ErenYagar/nvidia-lde-orcad-portfolio/evidence/stage3/3d_status.md

# Stage 3 RevK mechanical status

Disposition：`Digital_MCAD_Review_Complete_With_Explicit_Model_Blockers`

RevK native board SHA-256：`C772E9C3CD7A04A2CE3FBD1F5AE659E0935B786B235B17354DB83371BB4FF3EA`

RevK 3DX Canvas直接顯示：

- unplaced components 0/61；
- unrouted nets 0/54；
- unrouted connections 0/197；
- shape islands 0；
- unassigned shapes 0；
- DRC status up to date；DRC errors 0；shorting errors 0。

Assembly STEP：

- path：`manufacturing/stage3_final_revk/pcie_gen3_x4_nvme_adapter_reva_revk_final_preliminary.step`
- SHA-256：`DB176B106DC8D612EBFF79B8306FD327B831017CC22861F32DA83B99DF441EE0`
- size：8,939,536 bytes；
- format：STEP AP242；units：mm；datum：TOP/UPPER；
- isolated native DRA assignment/readback：`NATIVE_DRA_STEP_ASSIGNMENT_OK`。

`evidence/stage3/3dx_native_revk/`保存目前RevK工具畫面；`evidence/stage3/portfolio_revk/`的黑背景圖為presentation carry-forward。RevI到RevK之間的外部placement/model geometry未變，只有內層power connectivity vias與shape closure變更，因此可用於面試視覺，但不能當作exact-model collision Pass證據。

3D-01～3D-08仍依exact model可用性維持`Preliminary_Clear`或`Blocked_Missing_Exact_Model`。不宣稱PCIe compliance、fabrication release、chassis compatibility或bench qualification。
