ErenYagar/nvidia-lde-orcad-portfolio/evidence/stage3/final_release_status.md

# RevK final release status

`Interview_Digital_Complete` is achieved for the OrCAD digital portfolio.

`Fabrication_Ready` remains false because the project does not yet have the current fabricator stack-up, governing controlled specifications, frozen impedance geometry, exact mechanical context or physical bring-up evidence.

The digital closure is supported by the RevK native audits, current-board 3DX captures, AP242 STEP export and native re-import, engineering manufacturing outputs, PSpice failure/runtime-limit disclosure and hash-bound manifests.

No PCIe compliance, universal SSD support, chassis compatibility or bench qualification is claimed.
