ErenYagar/nvidia-lde-orcad-portfolio/evidence/stage3/stage3_delivery_gate.md

# Stage 3 RevK delivery gate

- Interview digital closure：`COMPLETE`
- Candidate status：`Interview_Digital_Complete_Not_For_Fabrication`
- Fabrication release：`BLOCKED`
- Native DRC：0
- Unconnected connections：0
- Active rats：0
- Unconnected PCIe nets：0
- Shape islands：0
- Unassigned shapes：0
- Native differential pairs：9（每組2 members）
- Pending fabricator geometry：9 pairs
- Exact-model collision blockers：仍存在
- PSpice governing recovery：`Simulated_Fail`（3.109 V）
- PSpice candidate sweep：27 × `Not_Concluded_Runtime_Limit`

## Digital gate results

- [x] RevK native board exists and is hash-bound。
- [x] DRC / connectivity / rats / PCIe connectivity closed。
- [x] L2/L5 GND與L4 power shapes implemented；zero islands。
- [x] 9 native differential pairs established。
- [x] Current RevK native 3DX evidence captured。
- [x] AP242/mm STEP generated and assigned/read back in isolated native DRA。
- [x] 14 Gerber、2 NC Drill、IPC-2581、BOM、P&P與CAM previews generated。
- [x] IPC-356 empty result excluded；ODB++ install limitation disclosed。
- [x] PSpice failure/runtime limitations disclosed without false pass。

## Fabrication blockers

- [ ] JLCPCB controlled-impedance stack-up archived。
- [ ] PCIe CEM/M.2 controlled specification sign-off completed。
- [ ] Pair width/gap/via geometry frozen in Constraint Manager。
- [ ] Exact mechanical models and 3D-01～3D-08 closure completed。
- [ ] Final CAM/DFM review after the above ECOs。
- [ ] Physical fabrication and bring-up completed。

Manufacturing files are engineering-review outputs only and must not be uploaded for fabrication while these gates remain open。
