ErenYagar/nvidia-lde-orcad-portfolio/portfolio/index.html

▰ EREN YAGAR / BOARD DESIGN

NVIDIA LDE INTERVIEW PORTFOLIO · REV K

# PCIe × NVMe without the black box.

A traceable OrCAD X / Allegro workflow for a six-layer PCIe Gen3 x4 add-in card to M.2 M-Key 2280 NVMe adapter.

See what it does ↘Read the case study ↗

INTERVIEW_DIGITAL_COMPLETE/Preliminary mechanical + digital review

FIG 01 / ASSEMBLY

120 × 64 MM · 6L

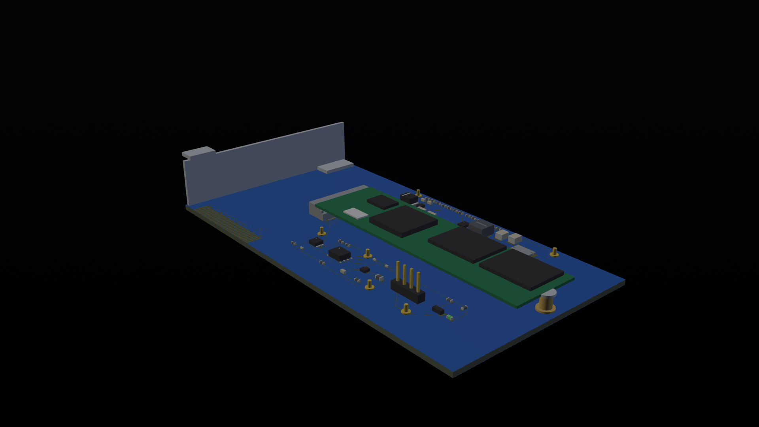
[picture p1: evidence/stage3/portfolio_revk/stage3_hero_isometric_assembly.png]
Isometric 3D assembly view of the PCIe to M.2 NVMe adapter board


06copper layers

×4PCIe Gen3 lanes

5A3.3 V normal target

09native pair objects

01 / SYSTEM FUNCTION

## A physical bridge, not a protocol box.

The host Root Complex and the NVMe controller remain the protocol endpoints. This board owns connection, power, telemetry and reviewable handoff.

HOSTPCIe Root ComplexJ1 edge · lanes / REFCLK

→

BOARDSix-layer interposerpower · sensing · placement

→

SSDM.2 M-Key 2280J2 · NVMe endpoint

01

### Signal continuity

Eight data pairs, REFCLK and sidebands are defined as a direct host-to-SSD path. No retimer, switch or packet conversion.

02

### Protected power

12 V slot input passes an eFuse, 6 A buck and 5 mΩ Kelvin shunt before the 3.3 V SSD branch.

03

### Observable rails

INA238 current and TMP1075 temperature paths reach a target-only I²C header with no external power back-feed.

04

### Explicit boundary

Digital closure is complete for the current board; compliance, chassis fit and bench qualification remain open.

02 / VISUAL EVIDENCE

## Designed to be inspected.

Portfolio views stay clean; engineering views, native reports and hashes remain in the repository.

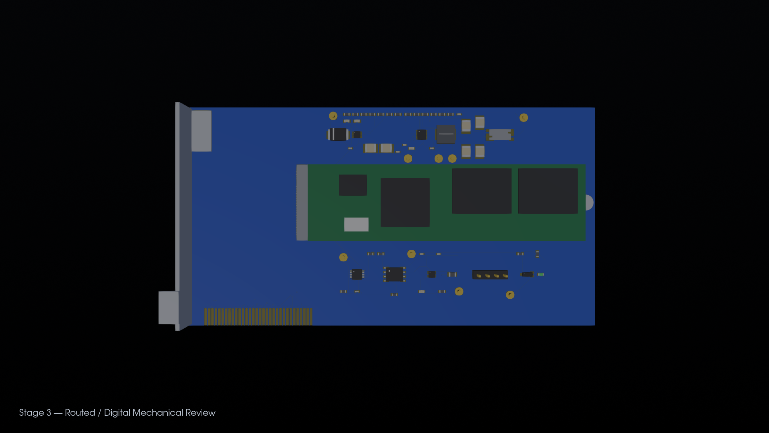
[picture p2: evidence/stage3/portfolio_revk/stage3_top_assembly.png]
Top assembly view showing M.2 slot, PCIe edge connector and component placement
 VIEW FULL ↗

02 / TOP ASSEMBLYConnector-first placement

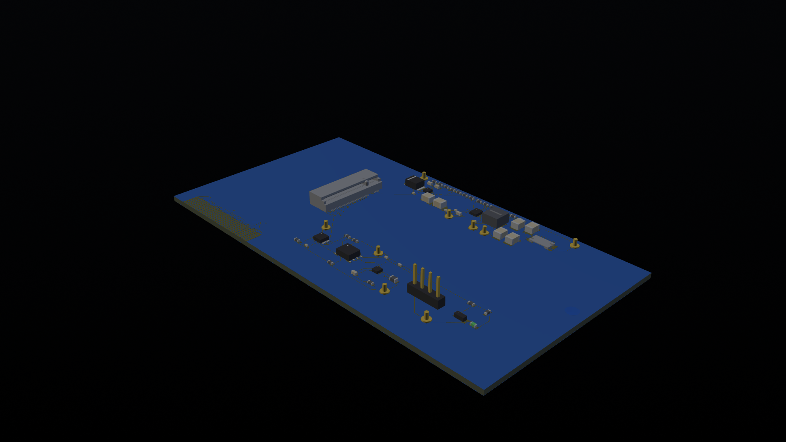
[picture p3: evidence/stage3/portfolio_revk/stage3_hero_isometric_pcb_detail.png]
Detailed isometric PCB view with component package models
 VIEW FULL ↗

03 / PACKAGE DETAILLibrary bodies, not blue blocks

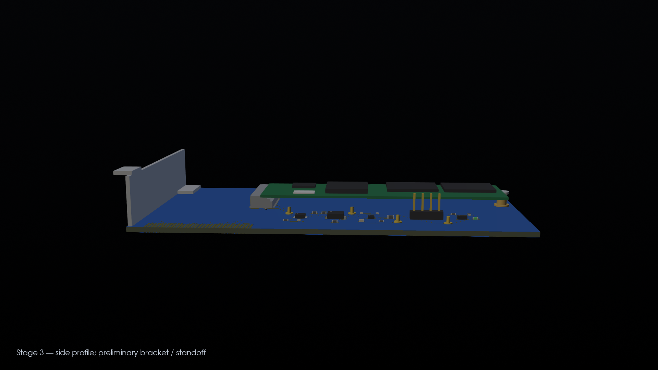
[picture p4: evidence/stage3/portfolio_revk/stage3_side.png]
Side view showing board thickness and low profile clearance
 VIEW FULL ↗

04 / SIDE REVIEWLow-profile baseline

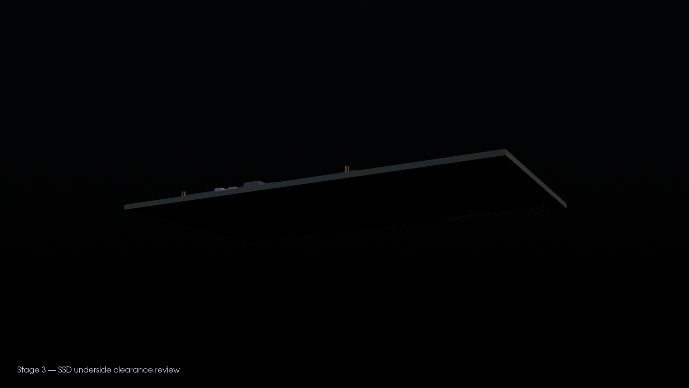
[picture p5: evidence/stage3/portfolio_revk/stage3_ssd_underside.png]
Underside view showing the SSD envelope and retention geometry
 VIEW FULL ↗

05 / UNDERSIDESSD envelope and retention

Open digital gate ↗Open native 3DX evidence ↗Open STEP status ↗

03 / ENGINEERING METHOD

## Every view has a paper trail.

The point is not to make uncertainty disappear; it is to make it findable.

01Power architecture

12 V + eFuse + buck was selected for review depth. The official buck profile records a 3.109 V recovery failure; no supported-SSD claim is inferred.

Read decision record ↗

02High-speed intent

Nine native differential-pair objects exist. Width, gap, via and skew remain pending the actual fabricator stack-up and controlled spec.

Read constraint status ↗

033DX / STEP handoff

Native 3DX views and AP242/mm STEP re-import are hash-bound to RevK. Missing exact models keep collision cases preliminary or blocked.

Read 3D status ↗

04Automation boundary

Python validators test CSV/report contracts and negative fixtures; they do not replace native Cadence review or bench data.

Read test harness ↗

CURRENT REVK SNAPSHOT

### Closed digitally. Open physically.

DRC / connectivity0 / 0 / 0

3DX / STEP loopRecorded

PSpice recovery3.109 V · fail

Stack-up / pin freezeOpen gate

ENGINEERING BOUNDARY

## Honest status is part of the design.

- Not a fabrication release or PCIe compliance claim.
- Controlled CEM/M.2 pin sources and JLCPCB stack-up remain gates.
- PSpice recovery and exact-model collision limits stay visible.

SOURCE-TRACEABLE / REVIEW-READY

## Bring the board into the interview.

Start with the function. Open the evidence when the conversation turns technical.

Use the interview guide ↗View GitHub portfolio ↗ (https://github.com/ErenYagar/nvidia-lde-orcad-portfolio)

© 2026 Eren YagarOrCAD X / Allegro / PSpice / 3DXRepository README ↗

×
