ErenYagar/nvidia-lde-orcad-portfolio/evidence/stage3/3dx_native_revk/revk_isometric_with_ui.png

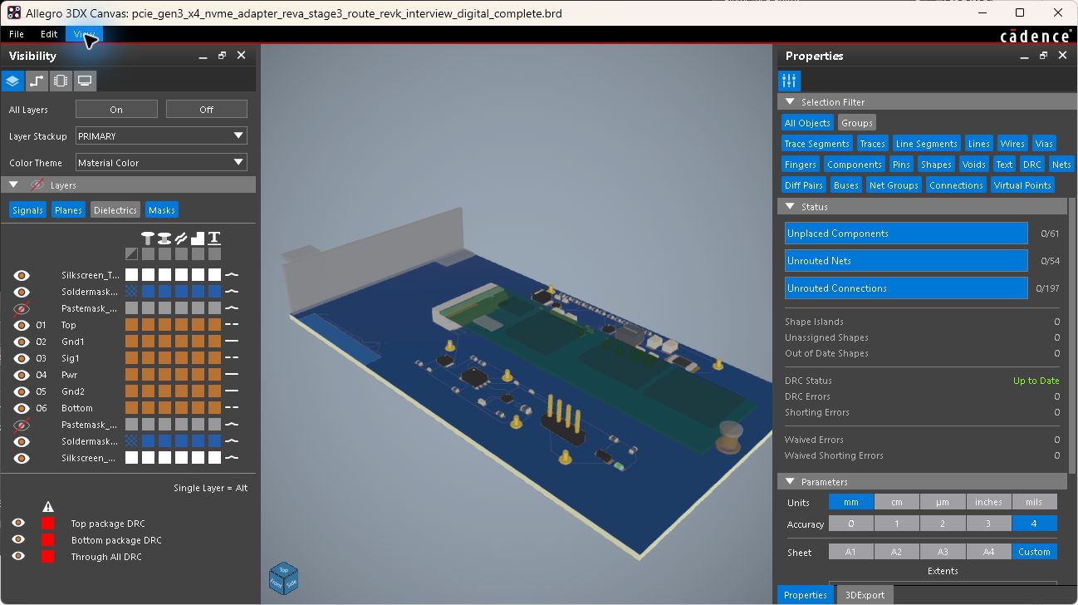
evidence/stage3/3dx_native_revk/revk_isometric_with_ui.png
