ErenYagar/nvidia-lde-orcad-portfolio/evidence/stage3/3dx_native_revk/revk_ssd_underside_bottom_iso_with_ui.png

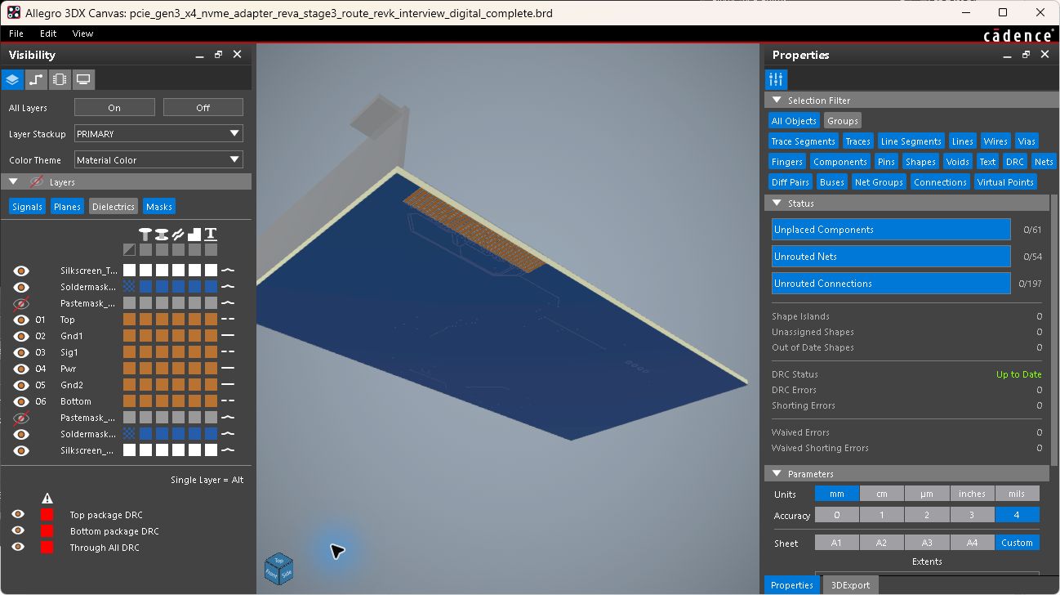
evidence/stage3/3dx_native_revk/revk_ssd_underside_bottom_iso_with_ui.png
