ErenYagar/nvidia-lde-orcad-portfolio/validation/supported_ssd_matrix.csv

Candidate_ID | Manufacturer | Exact_Model | Capacity_GB | Hardware_Revision | Firmware | Form_Factor | Steady_Current_A | Peak_Current_A | Peak_Duration_us | Power_Source_Type | Power_Source_Document | Power_Source_Revision | Power_Source_Date | Simulation_Evidence | Mechanical_Evidence | Bench_Evidence | Link_Evidence | Thermal_Evidence | Disposition | Exclusion_Reason | Reviewer | Review_Date | Official_Project_Status | Notes
WD-SN750-1TB-WDS100T3X0C | Western Digital | WDS100T3X0C | 1000 |  |  | M.2_2280_M_Key_NVMe |  | 2.8 | 10 | Official_Manufacturer | evidence/official_sources/WD_BLACK_SN750_Product_Brief_en_us.pdf | 02-05-WW-04-00054-A06 | 2021-09-01 | evidence/stage2/pspice/pw01_vendor_combined_run/pw01_window_metrics.csv |  |  |  |  | Candidate | Stage 2 PW-01 recovery minimum 3.109 V fails the 3.135 V screen; no support claim | Project | 2026-07-24 | Confirmed_Official | Stage 2 digital reference only; official brief confirms PCIe Gen3 x4 M.2 2280-S3-M 2.38 mm and 2.8 A peak for 10 us; candidate remains unqualified pending power-stage tuning and bench evidence
