ErenYagar/nvidia-lde-orcad-portfolio/evidence/stage3/portfolio_final_manifest.csv

Category | Path | Size_Bytes | SHA256 | Source_Board_SHA256 | Tool_Version | Export_Options | Artifact_State
Portfolio_View | evidence/stage3/portfolio_revk/stage3_bottom.png | 836241 | DD6D59DA8A34AD48E45E6F6496B7E7B3287F57D43F7E80EC34FC09076EDB2217 | C772E9C3CD7A04A2CE3FBD1F5AE659E0935B786B235B17354DB83371BB4FF3EA | Portfolio renderer | Black background; presentation carry-forward; external placement/models unchanged from RevI to RevK | Engineering_Assumption_Presentation_Only
Portfolio_View | evidence/stage3/portfolio_revk/stage3_bracket_review.png | 1134920 | 16A2DDD3E16E71FD604FCEED8EFF5096DB7E966670C49F217F7D0842DB3E07B3 | C772E9C3CD7A04A2CE3FBD1F5AE659E0935B786B235B17354DB83371BB4FF3EA | Portfolio renderer | Black background; presentation carry-forward; external placement/models unchanged from RevI to RevK | Engineering_Assumption_Presentation_Only
Portfolio_View | evidence/stage3/portfolio_revk/stage3_hero_isometric_assembly.png | 1068237 | 73D44483E89F8D3EC3DA486396125F33D81B8D2DE874CDA6AD81C6046A876B7F | C772E9C3CD7A04A2CE3FBD1F5AE659E0935B786B235B17354DB83371BB4FF3EA | Portfolio renderer | Black background; presentation carry-forward; external placement/models unchanged from RevI to RevK | Engineering_Assumption_Presentation_Only
Portfolio_View | evidence/stage3/portfolio_revk/stage3_hero_isometric_pcb_detail.png | 1047092 | 947E26D7545FA849B96110F3A6471BDFEC9349EE625C9F92349D176845722634 | C772E9C3CD7A04A2CE3FBD1F5AE659E0935B786B235B17354DB83371BB4FF3EA | Portfolio renderer | Black background; presentation carry-forward; external placement/models unchanged from RevI to RevK | Engineering_Assumption_Presentation_Only
Portfolio_View | evidence/stage3/portfolio_revk/stage3_side.png | 1122736 | AE649C2F9733FD281057A89A927F54B935771A81DF8F4056B75CFA0A47AC3A8A | C772E9C3CD7A04A2CE3FBD1F5AE659E0935B786B235B17354DB83371BB4FF3EA | Portfolio renderer | Black background; presentation carry-forward; external placement/models unchanged from RevI to RevK | Engineering_Assumption_Presentation_Only
Portfolio_View | evidence/stage3/portfolio_revk/stage3_ssd_underside.png | 1078659 | 9E7C0D50FCB859392D2BB6C93EDD4055487A906B86B05FCC9AA93C5AC043FF25 | C772E9C3CD7A04A2CE3FBD1F5AE659E0935B786B235B17354DB83371BB4FF3EA | Portfolio renderer | Black background; presentation carry-forward; external placement/models unchanged from RevI to RevK | Engineering_Assumption_Presentation_Only
Portfolio_View | evidence/stage3/portfolio_revk/stage3_top_assembly.png | 956764 | 278E7EC2BDE103E235BEA7C178F18A8CF67A20285036EA6B72F3E9F673CC8268 | C772E9C3CD7A04A2CE3FBD1F5AE659E0935B786B235B17354DB83371BB4FF3EA | Portfolio renderer | Black background; presentation carry-forward; external placement/models unchanged from RevI to RevK | Engineering_Assumption_Presentation_Only
Portfolio_View | evidence/stage3/portfolio_revk/stage3_top_pcb_detail.png | 941503 | 1F7E5A7ABA4ED7AF925F333A7F1F9B8C0B44121DCF040D93848C2527E408FFBA | C772E9C3CD7A04A2CE3FBD1F5AE659E0935B786B235B17354DB83371BB4FF3EA | Portfolio renderer | Black background; presentation carry-forward; external placement/models unchanged from RevI to RevK | Engineering_Assumption_Presentation_Only
