ErenYagar/nvidia-lde-orcad-portfolio/scripts/testdata/supported_ssd/valid/matrix.csv

Candidate_ID | Manufacturer | Exact_Model | Capacity_GB | Hardware_Revision | Firmware | Form_Factor | Steady_Current_A | Peak_Current_A | Peak_Duration_us | Power_Source_Type | Power_Source_Document | Power_Source_Revision | Power_Source_Date | Simulation_Evidence | Mechanical_Evidence | Bench_Evidence | Link_Evidence | Thermal_Evidence | Disposition | Exclusion_Reason | Reviewer | Review_Date | Official_Project_Status | Notes
TEST-CANDIDATE-01 | Example Storage | TEST-NVME-2280 | 1024 | A | TEST1 | M.2_2280_M_Key_NVMe | 4.0 | 6.0 | 100 | Official_Manufacturer | https://example.invalid/official-test-datasheet | TEST-REV-A | 2026-07-23 |  |  |  |  |  | Power_Screened |  |  |  | Confirmed_Official | Synthetic validator fixture only
TEST-EXCLUDED-01 | Example Storage | TEST-OVERLOAD | 2048 | A | TEST2 | M.2_2280_M_Key_NVMe | 5.5 | 8.0 | 150 | Official_Manufacturer | https://example.invalid/official-overload-test | TEST-REV-A | 2026-07-23 |  |  |  |  |  | Excluded | Exceeds project power envelope |  |  | Confirmed_Official | Synthetic validator fixture only
