ErenYagar/nvidia-lde-orcad-portfolio/scripts/testdata/stage2/invalid/missing_evidence/stage2/artifact_manifest.csv

Artifact | Path | Size_Bytes | SHA256 | Source_Path | Source_SHA256 | Status | Stage_State | Notes
Missing_Evidence | missing.bin | 1 | 0000000000000000000000000000000000000000000000000000000000000000 |  |  | Engineering_Assumption | Stage 2 - Batch Audited | Negative fixture
