ErenYagar/nvidia-lde-orcad-portfolio/scripts/testdata/stage2/invalid/stale_hash/stage2/artifact_manifest.csv

Artifact | Path | Size_Bytes | SHA256 | Source_Path | Source_SHA256 | Status | Stage_State | Notes
Stale_Hash | evidence.bin | 17 | 0000000000000000000000000000000000000000000000000000000000000000 |  |  | Engineering_Assumption | Stage 2 - Batch Audited | Negative fixture
