ErenYagar/nvidia-lde-orcad-portfolio/pcb/3d_models/stage3/harwin_s1751_46r.step

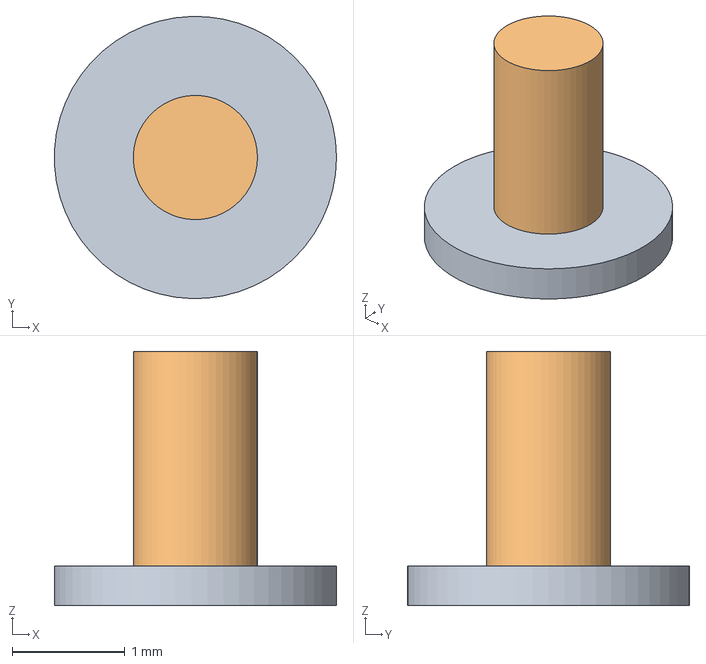
[picture p27: CAD file, 2026-07-27]
pcb/3d_models/stage3/harwin_s1751_46r.step
2.50 x 2.50 x 2.25 mm
