ErenYagar/nvidia-lde-orcad-portfolio/pcb/3d_models/stage3/r_0603_1608m.step

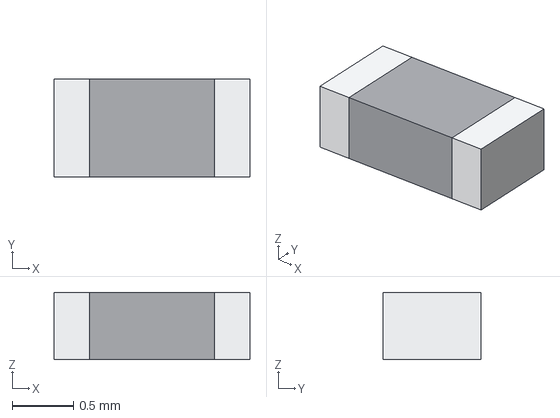
[picture p28: CAD file, 2026-07-27]
pcb/3d_models/stage3/r_0603_1608m.step
1.60 x 0.8 x 0.55 mm
