ErenYagar/nvidia-lde-orcad-portfolio/pcb/3d_models/stage3/c_1210_3225m.step

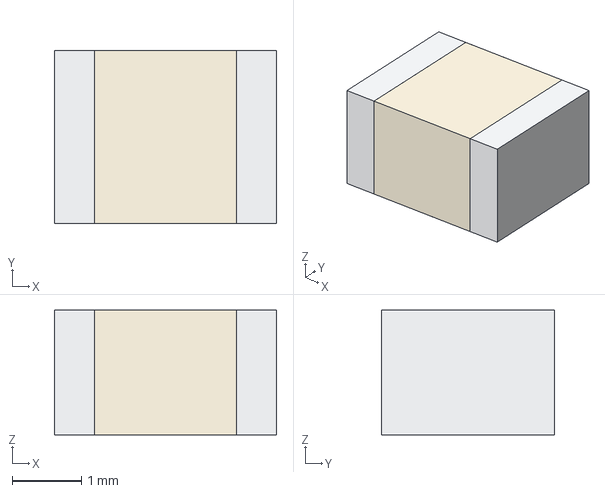
[picture p29: CAD file, 2026-07-27]
pcb/3d_models/stage3/c_1210_3225m.step
3.20 x 2.50 x 1.80 mm
