ErenYagar/nvidia-lde-orcad-portfolio/pcb/3d_models/stage3/hdr_1x4_2p54_ra.step

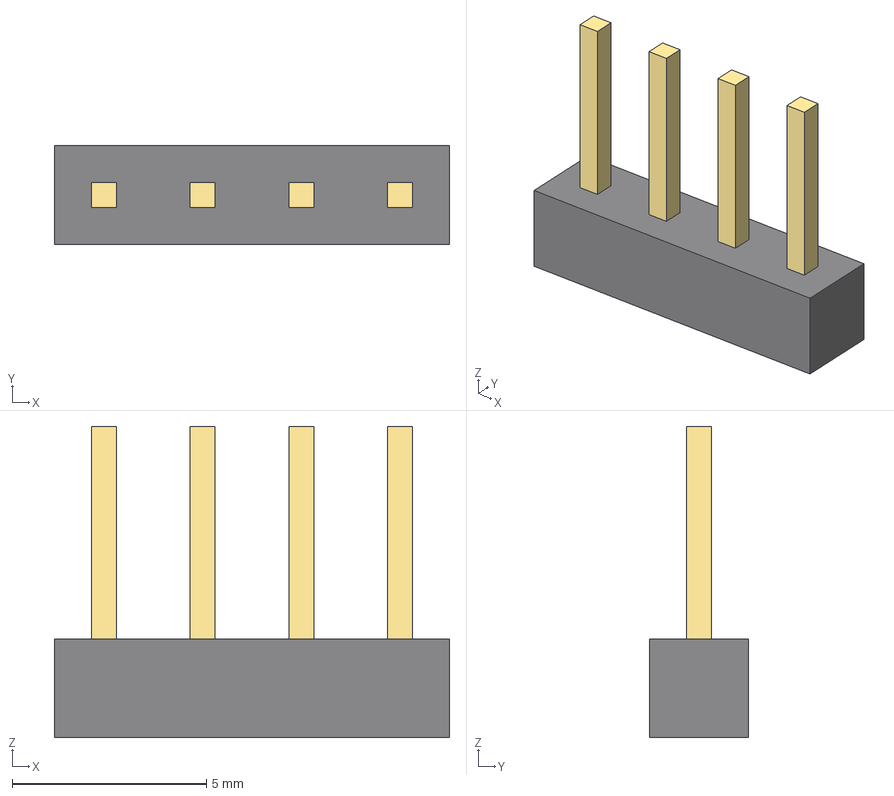
[picture p30: CAD file, 2026-07-27]
pcb/3d_models/stage3/hdr_1x4_2p54_ra.step
10.2 x 2.54 x 8.00 mm
