ErenYagar/nvidia-lde-orcad-portfolio/pcb/3d_models/stage3/low_profile_pcie_bracket_engineering.step

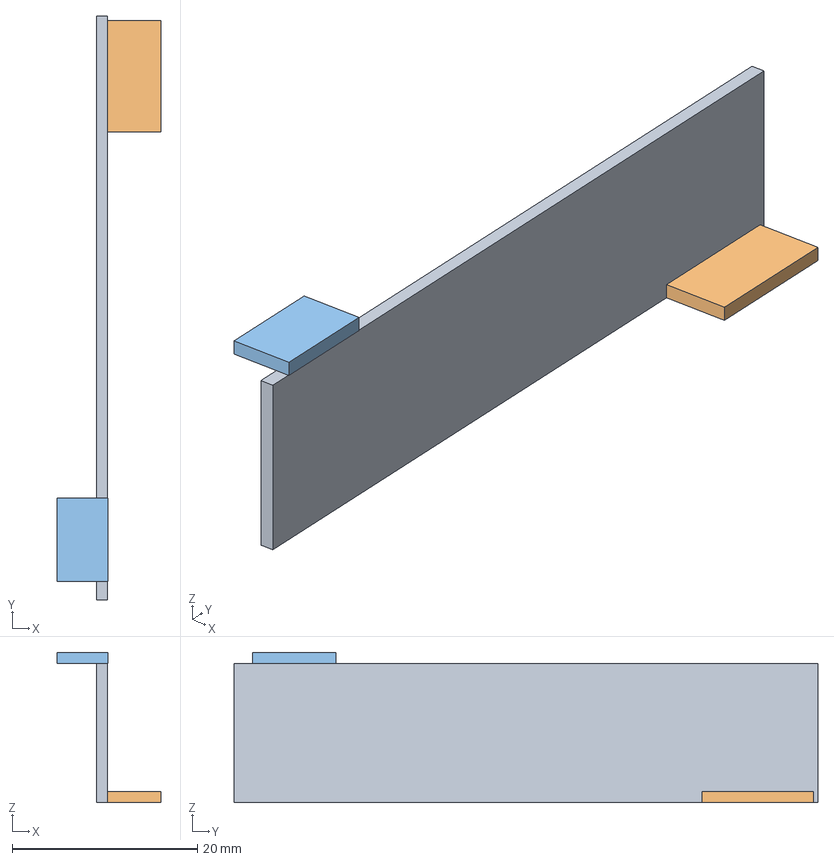
[picture p31: CAD file, 2026-07-27]
pcb/3d_models/stage3/low_profile_pcie_bracket_engineering.step
11.2 x 63.0 x 16.2 mm
