ErenYagar/nvidia-lde-orcad-portfolio/manufacturing/stage3_final_revk/cam_preview/revk_film_assembly_top_with_ui.png

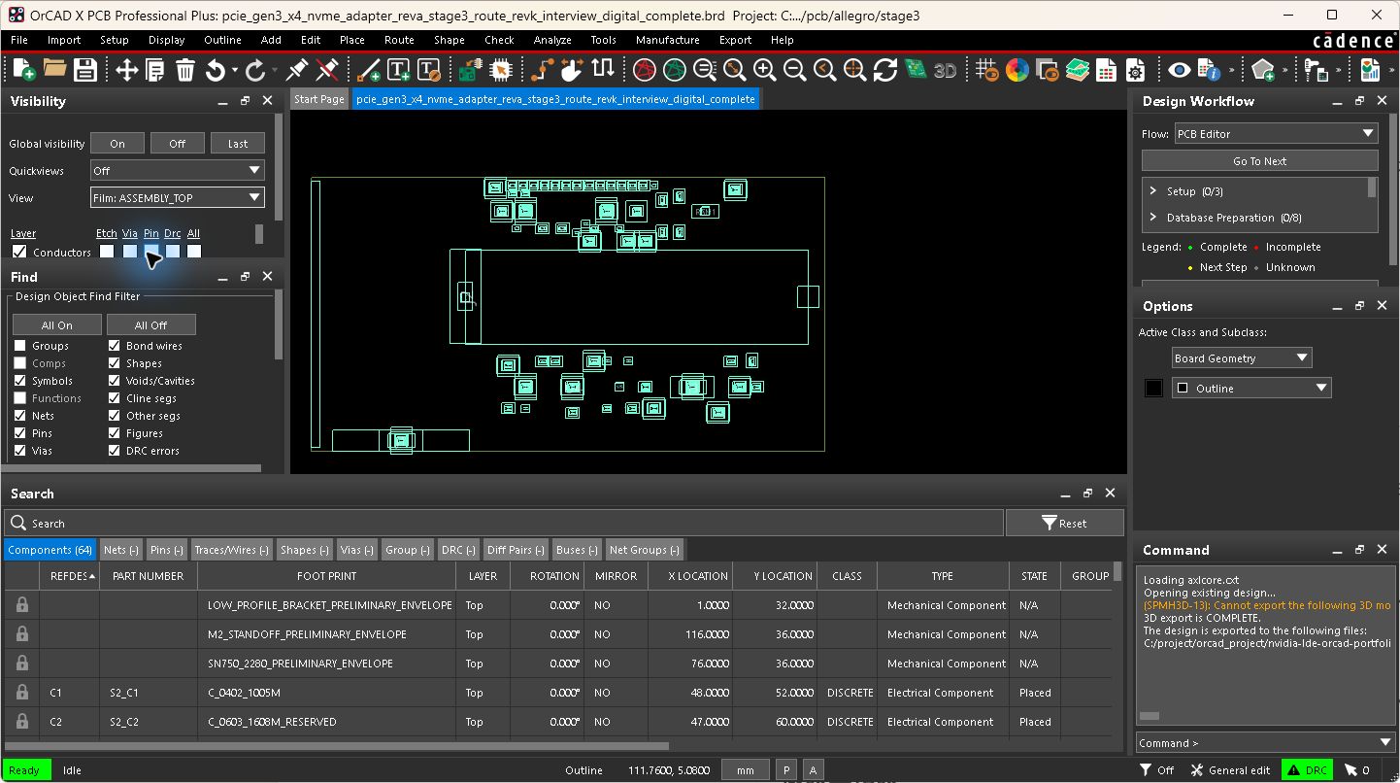
manufacturing/stage3_final_revk/cam_preview/revk_film_assembly_top_with_ui.png
