ErenYagar/nvidia-lde-orcad-portfolio/pspice/stage2/profile_results.csv

Profile_ID | Profile | Model | Input | Output | Raw_Result | Result | Status | Key_Observation | Limitations
ST-00 | Solver smoke test | PSpice primitive | evidence/stage2/batch/work/pspice_probe/pspice_probe.cir | evidence/stage2/batch/work/pspice_probe/pspice_probe.out | NA | Pass | Simulated | JOB CONCLUDED confirms the 25.1 command-line solver | Not a Rev A power-stage simulation
ST-02A | Buck startup through 820 us | TPS543620 SLUM787A | pspice/stage2/st02_buck_startup_820us.cir | pspice/stage2/st02_buck_startup_820us.out | pspice/stage2/st02_buck_startup_820us.csd | Partial_Startup_Concluded | Simulated | V(P3V3_NVME) final-window average 2.428 V while the 1 ms soft-start was still active | Does not evaluate steady state or the 7 A pulse
PW-01 | Combined startup and load sequence | TPS543620 SLUM787A | pspice/stage2/pw01_buck_combined_1400us.cir | pspice/stage2/pw01_buck_combined_1400us.out | pspice/stage2/pw01_buck_combined_1400us.csd | Fail_Recovery_Undershoot_5pct | Simulated | 5 A steady V(P3V3_NVME) minimum 3.149 V and 7 A/100 us minimum 3.204 V pass the 3.135 V screen; the recovery window minimum 3.109 V fails it while PGOOD remains high | Broad 5 A/7 A envelope is not qualified; peak inductor current reached 8.656 A; idealized macro-model omits layout and thermal effects; tune the power stage and rerun before any supported-SSD claim
LT-03S | Conservative 7 A charge-deficit capacitance sweep | PSpice primitive | evidence/stage2/batch/lt03_charge_deficit_summary.csv | evidence/stage2/batch/lt03_charge_deficit_summary.csv | evidence/stage2/batch/work/lt03_charge_deficit/ | Completed_Screen | Simulated | Six effective-Cout cases preserve the raw CSDF and threshold result | Not the official TPS543620 macro-model
EF-01 | eFuse isolated startup | TPS25947x SLVMDJ6A | pspice/smoke_tests/tps25947_vendor_reference/ | pspice/smoke_tests/tps25947_vendor_reference/run_record.md | pspice/smoke_tests/tps25947_vendor_reference/ | Fail_Functional_Validation | Pending_Human_Verification | Encrypted model loaded but retained runs did not reach a valid output startup | No eFuse startup inrush or latch-off claim
AC-01 | Loop stability | TPS543620 SLUM787A | NA | pspice/simulation_plan.md | NA | Not_Supported_By_Model | Planned | Transient encrypted model has no supported average or small-signal path | Requires another model or physical Bode measurement
MC-01 | Monte Carlo | TPS543620 SLUM787A | NA | pspice/simulation_plan.md | NA | Not_Supported_By_Model | Planned | No validated statistical parameters are exposed | Deterministic corners remain the supported fallback
