ErenYagar/nvidia-lde-orcad-portfolio/validation/validation/test_matrix.csv

Test_ID | Phase | Category | Test_Name | Preconditions | Procedure | Instrument_or_Tool | Expected_Result | Pass_Fail_Criteria | Validation_Status | Evidence_File | Notes
VAL-001 | Pre-power | Mechanical | Visual inspection | Bare assembled card and drawings available | Inspect orientation solder joints contamination fingers connector and mounting | Microscope and assembly drawing | No visible assembly defect | No bridge wrong polarity damaged finger or mechanical interference | Planned | TBD_AFTER_TEST | Do not install SSD
VAL-002 | Pre-power | Power | Resistance to GND without SSD | Card unpowered and discharged | Measure P12V_SLOT P12V_PROTECTED and P3V3_NVME to GND both polarities | DMM | No hard short and readings are recorded | No near-zero stable resistance unless explained by circuit | Planned | TBD_AFTER_TEST | Absolute value is not predetermined
VAL-003 | Pre-power | Power | Current-limited bench startup | Host disconnected and SSD absent | Feed protected 12V injection point using documented current limit | Bench supply and DMM | Controlled startup without current-limit latch | No smoke overheating or unexplained current limit | Planned | TBD_AFTER_TEST | Injection method requires schematic review
VAL-004 | Power | Power | 3.3V rail startup | VAL-003 passed | Capture P3V3_NVME and PGOOD during power-on | Oscilloscope with short ground spring | Rail starts monotonically and PGOOD follows configured threshold | Measured waveform meets approved PSpice-derived limits | Planned | TBD_AFTER_TEST | Limits frozen only after simulation
VAL-005 | Power | Power | Static no-load current | SSD absent and rail stable | Measure 12V input and 3.3V no-load current | Bench supply or current probe | Current is stable and explainable | Value within calculated no-load budget plus approved tolerance | Planned | TBD_AFTER_TEST | No fabricated expected number
VAL-006 | Power | Power | Output ripple without SSD | VAL-004 passed | Measure AC-coupled ripple at shunt load side | Oscilloscope and bandwidth-limit setup | No burst or instability inconsistent with selected mode | Ripple within final power requirement | Planned | TBD_AFTER_TEST | Record probe method and bandwidth
VAL-007 | Telemetry | I2C | INA238 discovery | 3.3V stable and external I2C master connected | Scan only approved address then read manufacturer or configuration register | I2C adapter and logic analyzer | Device acknowledges at strapped address | Expected address ACK and no bus contention | Planned | TBD_AFTER_TEST | Header must not back-power board
VAL-008 | Telemetry | I2C | TMP1075 discovery | VAL-007 bus integrity passed | Read temperature register and compare with ambient reference | I2C adapter and thermometer | Reading is plausible and stable | Within datasheet-informed acceptance band after stabilization | Planned | TBD_AFTER_TEST | Not a calibrated thermal test
VAL-009 | Power | SSD | SSD startup current | Power tests passed and approved SSD installed | Cold-start while capturing input output current voltage and PGOOD | Oscilloscope current probe and telemetry | No brownout or protection nuisance trip | Waveforms meet frozen droop timing and current-limit criteria | Planned | TBD_AFTER_TEST | Record exact SSD model and firmware
VAL-010 | System | Host | Host insertion safety | Host off and card inspected | Install card and confirm bracket seating and connector engagement | Visual inspection | Card seats fully without flex or interference | No mechanical conflict and host remains safe | Planned | TBD_AFTER_TEST | Host power remains off during installation
VAL-011 | PCIe | Enumeration | PCIe enumeration | VAL-010 complete and host powered | Boot OS and capture lspci dmesg or Device Manager evidence | Linux or Windows host | NVMe endpoint enumerates once without repeated link reset | Device visible with stable BDF and no fatal PCIe error | Planned | TBD_AFTER_TEST | Does not imply compliance
VAL-012 | PCIe | Link | Link speed | Endpoint enumerated | Capture LnkCap and LnkSta with lspci -vv | Linux lspci | Negotiated speed is recorded | Gen3 only passes when host slot and SSD both support Gen3 and link is stable | Planned | TBD_AFTER_TEST | Lower speed triggers fault tree
VAL-013 | PCIe | Link | Link width | Endpoint enumerated | Capture LnkCap and LnkSta with lspci -vv | Linux lspci | Negotiated width is recorded | x4 only passes when host slot and SSD support x4 and all lanes are intact | Planned | TBD_AFTER_TEST | x1 or x2 triggers lane diagnosis
VAL-014 | NVMe | Protocol | NVMe identify | Enumeration stable | Run nvme list and nvme id-ctrl or Windows equivalent | nvme-cli or vendor tool | Controller identity and namespace are readable | Commands complete without timeout or reset | Planned | TBD_AFTER_TEST | Save command output
VAL-015 | Storage | Functional | Short read write | Test drive contains disposable data | Run bounded verified read/write workload on test namespace | fio or CrystalDiskMark | Workload completes without I/O or PCIe error | Zero unplanned reset and verification error | Planned | TBD_AFTER_TEST | Never run destructive workload on user data
VAL-016 | Storage | Stress | Long duration stress | Short test passed and cooling configuration documented | Run staged workload while logging power temperature SMART and kernel events | fio smartctl telemetry and logger | No unplanned disappearance error or thermal emergency | Criteria defined in storage_stress_test.md before run | Planned | TBD_AFTER_TEST | Use FIO-RANDREAD-STRESS then separately approved FIO-MIXED-STRESS from test_profiles.csv
VAL-017 | Thermal | Thermal | Basic thermal survey | Stress workload stable | Record SSD buck eFuse shunt inlet and ambient temperature | Thermocouple or calibrated IR setup | Temperature reaches stable or bounded trend | All parts stay inside approved derated limits | Planned | TBD_AFTER_TEST | Emissivity and sensor location recorded
VAL-018 | System | Power cycle | Cold boot repeatability | All prior functional tests passed | Perform documented count of full power removals and boots | Host log and power control | Enumeration succeeds consistently | Zero failure in predeclared trial count | Planned | TBD_AFTER_TEST | Use BOOT-COLD-10 from test_profiles.csv
VAL-019 | System | Reset | Warm boot repeatability | All prior functional tests passed | Perform documented count of OS restarts and resets | Host log | Endpoint returns after each warm boot | Zero failure in predeclared trial count | Planned | TBD_AFTER_TEST | Use BOOT-WARM-10 from test_profiles.csv and keep evidence separate from cold boot
VAL-020 | Compatibility | SSD | Second SSD compatibility | First SSD baseline complete | Repeat minimum power enumeration and link suite with second approved SSD | Same equipment as baseline | Results recorded per SSD | No safety fault and deviations explained | Planned | TBD_AFTER_TEST | Not a universal compatibility claim
VAL-021 | Debug | ECO | Failure and ECO closure | Any anomaly has been observed | Create debug log root-cause evidence and ECO impact assessment | Lab instruments and templates | Anomaly is reproducible or explicitly closed as not reproduced | ECO has verification plan and regression scope | Planned | TBD_AFTER_TEST | Do not assign root cause without evidence
