ErenYagar/nvidia-lde-orcad-portfolio/validation/validation/test_profiles.csv

Profile_ID | Related_Test_ID | Host_OS | Phase | Workload | Access_Mode | Target_Scope | Runtime_s | Block_Size | Queue_Depth | Verify_Mode | Trial_Count | Safety_Gate | Stop_Conditions | Evidence_Prefix | Status | Notes
ENUM-LINUX-01 | VAL-011;VAL-012;VAL-013;VAL-014 | Linux | Enumeration | lspci and NVMe identify | Read_Only | Exact BDF and controller selected before capture | NA | NA | NA | NA | 1 | Preserve kernel log before and after without clearing it | Fatal AER or repeated controller reset | ENUM_LINUX_01 | Planned | Does not imply PCIe compliance
BOOT-COLD-10 | VAL-018 | Linux_or_Windows | Repeatability | Full power removal and boot | Read_Only | Approved host card and exact SSD | NA | NA | NA | NA | 10 | All prior functional tests passed and trial count frozen before run | Any smoke rail fault fatal AER or data error | BOOT_COLD_10 | Planned | Ten trials are an internal engineering test-plan choice rather than a specification requirement
BOOT-WARM-10 | VAL-019 | Linux_or_Windows | Repeatability | OS restart and endpoint return | Read_Only | Approved host card and exact SSD | NA | NA | NA | NA | 10 | All prior functional tests passed and cold and warm logs remain separate | Any rail fault fatal AER controller loss or data error | BOOT_WARM_10 | Planned | Ten trials are an internal engineering test-plan choice rather than a specification requirement
FIO-READ-SHORT | VAL-015 | Linux | Short_functional | Sequential read | Read_Only | Exact approved test namespace | 60 | 128k | 8 | None | 1 | Run parse-only first and retain fio readonly guard | I/O error controller reset rail violation or thermal stop | FIO_READ_SHORT | Planned | Runtime and workload are Engineering_Assumption test settings
FIO-WRITE-VERIFY-SHORT | VAL-015 | Linux | Short_functional | Sequential write plus verify | Destructive_Write | Disposable isolated test namespace only | 60 | 128k | 8 | crc32c | 1 | Written authorization exact namespace cross-check unmounted target backup confirmation and reviewed job file | I/O verification error controller reset rail violation or thermal stop | FIO_WRITE_VERIFY_SHORT | Planned | No executable write command is supplied in repository documentation
FIO-RANDREAD-STRESS | VAL-016 | Linux | Stress | Random read | Read_Only | Exact approved test namespace | 1800 | 4k | 32 | None | 1 | Short functional case passed then run parse-only and retain fio readonly guard | I/O error controller reset rail violation thermal stop or SMART critical warning | FIO_RANDREAD_STRESS | Planned | Thirty minutes is an internal Stage-1 stress setting and not a qualification standard
FIO-MIXED-STRESS | VAL-016 | Linux | Stress | Mixed read and write | Destructive_Write | Disposable isolated test namespace only | 1800 | 4k | 32 | crc32c | 1 | Write authorization and all short read and write cases passed with approved cooling and evidence capture | I/O verification error controller reset rail violation thermal stop or SMART critical warning | FIO_MIXED_STRESS | Planned | No executable write command is supplied until target approval
