ErenYagar/nvidia-lde-orcad-portfolio/pspice/stage3/recovery_sweep/recovery_sweep_results.csv

Case_ID | COUT_EFF_uF | ESR_mOhm | CFF_pF | Timeout_s | Elapsed_s | Exit_Code | Disposition | OUT_Bytes | CSD_Bytes | Circuit_SHA256 | OUT_SHA256 | CSD_SHA256 | Status
cout100u_esr2m_cff0p0p | 100 | 2 | 0.0 | 15 | 15.273 |  | Not_Concluded_Runtime_Limit | 1201 | 958464 | 3A29FE5A873C2CAE95AFD42A63F8272D545E3C253B957C669CA52E13EDEC9F9C | AE3F4DB28F5FB330E624A588B72C33FBC10C918C6ACFBDFFC63503995EBC3B57 | 24AD2F69359D50225E351DBD156CF2039D20E0230BFCAE773EE08A5834A9667E | Simulated
cout100u_esr2m_cff4p7p | 100 | 2 | 4.7 | 15 | 15.342 |  | Not_Concluded_Runtime_Limit | 1223 | 925696 | E76F21F14D5DDA6021465F5D85FDC17544FB773C4DFA6A821151237BD15A193A | 40B9E5EC98ACA3C31EC12DB11CAD2B9219E84A6E00B3A7E636427745E5C9AE98 | 58F5146A457FA796C62E383CEFE940E117E897FED5A36D68EBD67CCC1D9454A4 | Simulated
cout100u_esr2m_cff8p2p | 100 | 2 | 8.2 | 15 | 15.485 |  | Not_Concluded_Runtime_Limit | 1223 | 925696 | 0DE0E19BB296DE0F2CF581630678F94171D7EA6A8798C27D1DAB1B218959F2B6 | 896EDAD7EFCE6943FCDB55D65BE5695CF510A78599A1B2E9D4252911708A9AF7 | 7C7BA9007F0B1AFF4CE8179ECBCDC4CFBC9AACEBE5F9B715BB9AC7D827B6AD5B | Simulated
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
