ErenYagar/nvidia-lde-orcad-portfolio/scripts/testdata/stage2/valid/delivery_status.csv

Item | State | Evidence | Status | Notes
Routing | Not_Started | evidence.txt | Planned | Placed and unrouted
Fabrication_Release | Not_Released | evidence.txt | Planned | Not a fabrication release
PCIe_Compliance | Not_Claimed | evidence.txt | Not_Yet_Measured | No compliance claim
