ErenYagar/nvidia-lde-orcad-portfolio/scripts/testdata/stage2/invalid/routing_claim/delivery_status.csv

Item | State | Evidence | Status | Notes
Routing | Pass | evidence.txt | Confirmed_Official | False routing pass
Fabrication_Release | Not_Released | evidence.txt | Planned | Not a fabrication release
PCIe_Compliance | Not_Claimed | evidence.txt | Not_Yet_Measured | No compliance claim
